gg881/Calorimetro/Inventor/tampa-baixo.dxf

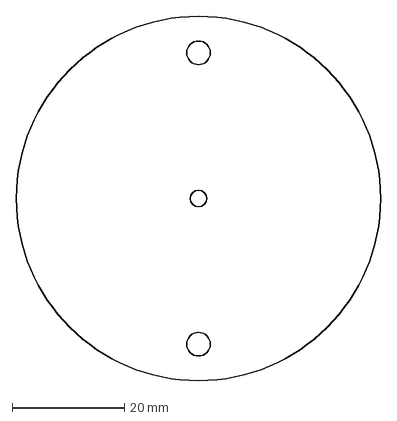
[picture p54: CAD file, 2022-08-01]
Inventor/tampa-baixo.dxf
65.0 x 65.0 mm
