gg881/Calorimetro/Inventor/face_superior.dxf

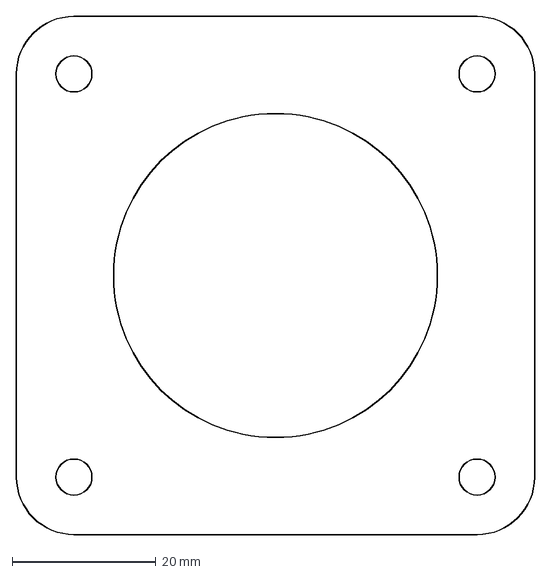
[picture p56: CAD file, 2022-08-01]
Inventor/face_superior.dxf
72.0 x 72.0 mm
