gg881/Calorimetro/Inventor/suporte_fechamento_tipo2a.stl

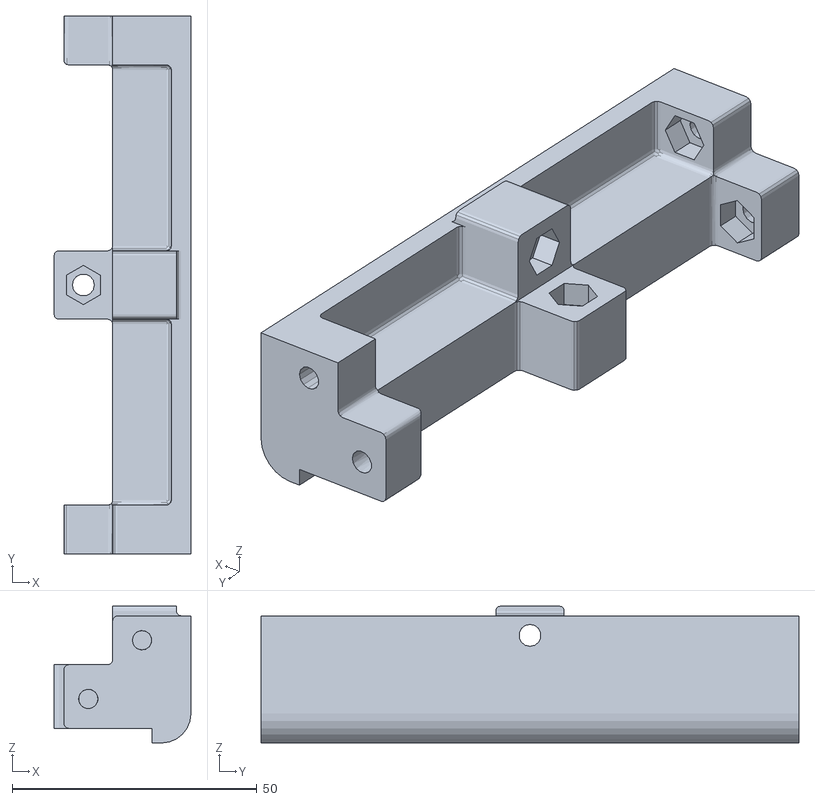
[picture p57: CAD file, 2022-08-01]
Inventor/suporte_fechamento_tipo2a.stl
28.0 x 110.0 x 28.0
