gg881/Calorimetro/Inventor/face_baixo.dxf

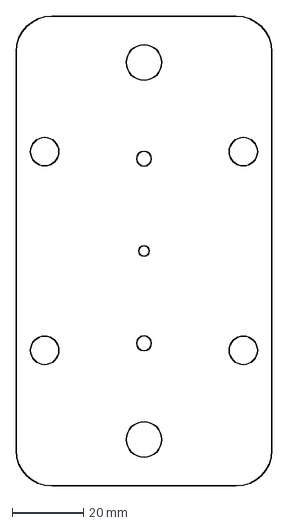
[picture p58: CAD file, 2022-08-01]
Inventor/face_baixo.dxf
72.0 x 132.4 mm
