gg881/Calorimetro/Inventor/tampa.dxf

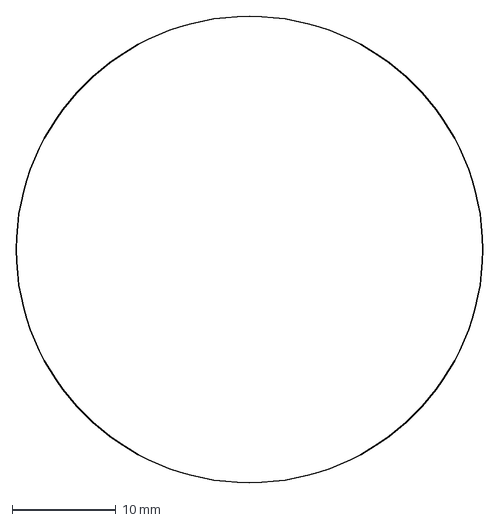
[picture p59: CAD file, 2022-08-01]
Inventor/tampa.dxf
44.9 x 44.9 mm
